wayneballard/Temperature-measurement-station/KiCad/project_schematic.kicad_sch

## KiCad design KiCad/project_schematic.kicad_sch (2025-10-18)

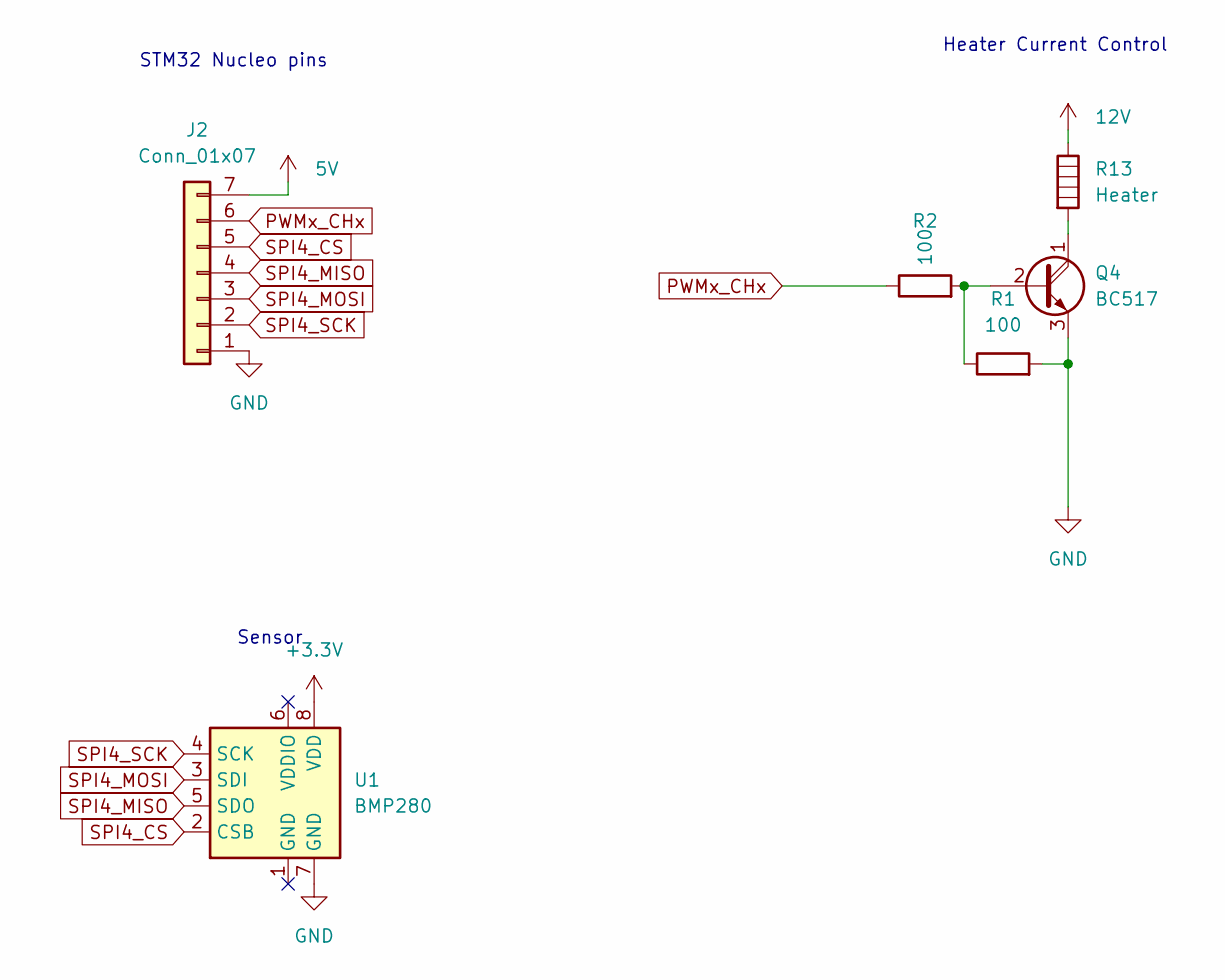
[picture p8: schematic project_schematic.kicad_sch]

Parts:
J2: Conn_01x07
Q4: BC517; TO-92_Inline
R1, R2: 100
R13: Heater
U1: BMP280; Bosch_LGA-8_2x2.5mm_P0.65mm_ClockwisePinNumbering

Connections:
5V: J2.7
12V: R13.1
+3.3V: U1.8 (VDD)
GND: J2.1, Q4.3 (E), R1.2, U1.7 (GND)
unnamed: Q4.1 (C), R13.2
unnamed: Q4.2 (B), R1.1, R2.2
PWMx_CHx: J2.6, R2.1
SPI4_CS: J2.5, U1.2 (CSB)
SPI4_MISO: J2.4, U1.5 (SDO)
SPI4_MOSI: J2.3, U1.3 (SDI)
SPI4_SCK: J2.2, U1.4 (SCK)

Notes on the sheet:
Heater Current Control
STM32 Nucleo pins
Sensor
