wayneballard/Temperature-measurement-station/STM32CubeIDE/Components/Src/heater_config.c

/**
  ******************************************************************************
  * @file		  : heater_config.c
  * @author  	: AW		Adrian.Wojcik@put.poznan.pl
  * @version 	: 1.3.0
  * @date     : Nov 27, 2022
  * @brief    : Electric heater components configuration file
  *
  ******************************************************************************
  */

/* Private includes ----------------------------------------------------------*/
#include "heater.h"
#include "tim.h"

/* Private typedef -----------------------------------------------------------*/

/* Private define ------------------------------------------------------------*/

/* Private macro -------------------------------------------------------------*/

/* Private variables ---------------------------------------------------------*/

/* Public variables ----------------------------------------------------------*/

/* Private function prototypes -----------------------------------------------*/

/* Public function prototypes ------------------------------------------------*/

/* Private functions ---------------------------------------------------------*/

/* Public functions ----------------------------------------------------------*/
