wayneballard/Temperature-measurement-station/STM32CubeIDE/Components/Inc/heater_config.h

/*
 * heater_config.h
 *
 *  Created on: Jan 25, 2025
 *      Author: limok
 */

#ifndef INC_HEATER_CONFIG_H_
#define INC_HEATER_CONFIG_H_

#include "heater.h"

extern HEATER_PWM_Handle_TypeDef hheater;


#endif /* INC_HEATER_CONFIG_H_ */
